thomai-d/MonoTon/src/MonoTon/Configuration.h

#pragma once

#define SAMPLE_RATE	20000
#define CONTROL_RATE 50
#define CONTROL_RATE_MS (1000 / CONTROL_RATE)
#define BUTTON_DEBOUNCE_MILLIS 20

#define MIN_BPM		90
#define DEFAULT_BPM	120
#define MAX_BPM		180

#define MAX_CHANNELS	8
#define MAX_STEPS		16	
#define MAX_PARAMETERS	4	
#define MAX_BANKS		4

#define PARAMETER_DISPLAY_TIME_MS	500
