thomai-d/MonoTon/src/MonoTon/System/TimerThree.cpp

/*
 *  Interrupt and PWM utilities for 16 bit Timer3 on ATmega168/328
 *  Original code by Jesse Tane for http://labs.ideo.com August 2008
 *  Modified March 2009 by Jérôme Despatis and Jesse Tane for ATmega328 support
 *  Modified June 2009 by Michael Polli and Jesse Tane to fix a bug in setPeriod() which caused the timer to stop
 *  Modified Oct 2009 by Dan Clemens to work with timer3 of the ATMega1280 or Arduino Mega
 *
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
 */

#include "TimerThree.h"

TimerThree Timer3;

ISR(TIMER3_OVF_vect)          // interrupt service routine that wraps a user defined function supplied by attachInterrupt
{
  Timer3.isrCallback();
}

void TimerThree::initialize(long microseconds)
{
  TCCR3A = 0;                 // clear control register A 
  TCCR3B = _BV(WGM13);        // set mode as phase and frequency correct pwm, stop the timer
  setPeriod(microseconds);
}

void TimerThree::setPeriod(long microseconds)
{
  long cycles = (F_CPU * microseconds) / 2000000;                                // the counter runs backwards after TOP, interrupt is at BOTTOM so divide microseconds by 2
  if(cycles < RESOLUTION)              clockSelectBits = _BV(CS10);              // no prescale, full xtal
  else if((cycles >>= 3) < RESOLUTION) clockSelectBits = _BV(CS11);              // prescale by /8
  else if((cycles >>= 3) < RESOLUTION) clockSelectBits = _BV(CS11) | _BV(CS10);  // prescale by /64
  else if((cycles >>= 2) < RESOLUTION) clockSelectBits = _BV(CS12);              // prescale by /256
  else if((cycles >>= 2) < RESOLUTION) clockSelectBits = _BV(CS12) | _BV(CS10);  // prescale by /1024
  else        cycles = RESOLUTION - 1, clockSelectBits = _BV(CS12) | _BV(CS10);  // request was out of bounds, set as maximum
  ICR3 = pwmPeriod = cycles;                                                     // ICR1 is TOP in p & f correct pwm mode
  TCCR3B &= ~(_BV(CS10) | _BV(CS11) | _BV(CS12));
  TCCR3B |= clockSelectBits;                                                     // reset clock select register
}

void TimerThree::attachInterrupt(void (*isr)(), long microseconds)
{
  if(microseconds > 0) setPeriod(microseconds);
  isrCallback = isr;                                       // register the user's callback with the real ISR
  TIMSK3 = _BV(TOIE1);                                     // sets the timer overflow interrupt enable bit
  sei();                                                   // ensures that interrupts are globally enabled
  start();
}

void TimerThree::detachInterrupt()
{
  TIMSK3 &= ~_BV(TOIE1);                                   // clears the timer overflow interrupt enable bit 
}

void TimerThree::start()
{
  TCCR3B |= clockSelectBits;
}

void TimerThree::stop()
{
  TCCR3B &= ~(_BV(CS10) | _BV(CS11) | _BV(CS12));          // clears all clock selects bits
}

void TimerThree::restart()
{
  TCNT3 = 0;
}
